MohammadAbbasi76/voice_recorder_with_stm32f103/MySource/Component/VoiceRecorder/inc/TypeDefine.h

#ifndef __TYPEDEF_H_
#define __TYPEDEF_H_
#include <string.h>
#include <stdarg.h>
#include <stdbool.h>
#include <stdio.h>
#include "main.h"
#include "tim.h"
#include "adc.h"
#include "usart.h"
#include "stm32f1xx_hal_gpio.h"

#include "RecordFunctions.h"
#include "PlaysFunctions.h"
#include "WriteToFlash.h"

#include "w25qxx.h"
#include "ReadKeyboard.h"
#include "SevenSegmentAnd_LEDS.h"
#include "STM_Log.h"

#define StopTimeInSec 10
#define GO_TO_FACTORYRESET_MODE_TIME 5000

uint16_t Buffer1[VoiceArraySize];
uint16_t Buffer2[VoiceArraySize];

typedef enum
{
    Init,
    RecordState,
    PlayState,
    PauseState,
    StopRecordingState,
    StopPlayingState,
    NextTrackState,
    ReadKeyboardState,
    FlashEraseState
} state_t;
typedef struct
{
    uint32_t Counter;
    uint32_t TotallyStopTim;
    uint32_t StopTimeCounter;
} ADC_St;
typedef struct
{
    uint32_t Counter;
    uint32_t CountDataFromTotally[MaxNumberOfVoice];
} PWM_St;
typedef struct
{
    uint8_t CountOfSavedArray;
    uint8_t RecordedArray[MaxNumberOfVoice];
} Voice_St;
typedef struct
{
    uint8_t AdcArrayFull;
    uint8_t InterruptSwitch;
    uint8_t PwmArrayEmpty;
} Flags_St;
typedef enum
{
    ResetFactory,
    NormalMode
} DeviceMode_t;

typedef struct
{
    ADC_St ADC;
    PWM_St PWM;
    Flags_St Flag;
    Voice_St Voice;
    uint8_t Track;
    uint8_t ReadFromFlash;
    uint8_t State;
    uint8_t DeviceMode;
} VoiceRecorder_St;
VoiceRecorder_St VoiceRecorderSt;
#endif
