MohammadAbbasi76/voice_recorder_with_stm32f103/MySource/Component/VoiceRecorder/inc/VoiceRecorderInterface.h

#ifndef VOICE_RECORDER_H
#define VOICE_RECORDER_H

#include"TypeDefine.h"




void RestFactoryFunction();
void ChooseVoiceForPlay();
void NextTrack();
void DummyFunc();
void InterruptFunc();
void VoiceRecorder();
void VoiceRecorderInitiation();

#endif
